michaelpmurphy14/AirQ-automation/Esp32C3 Project/3D Images/Renderred Back.png

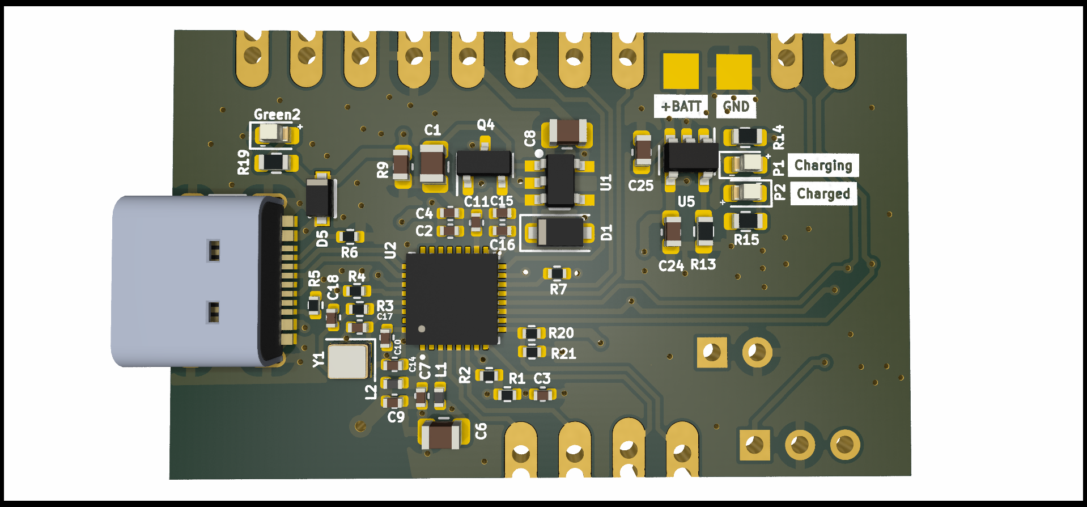
Esp32C3 Project/3D Images/Renderred Back.png
