michaelpmurphy14/AirQ-automation/CO Sensor PCB/PCB Layout.png

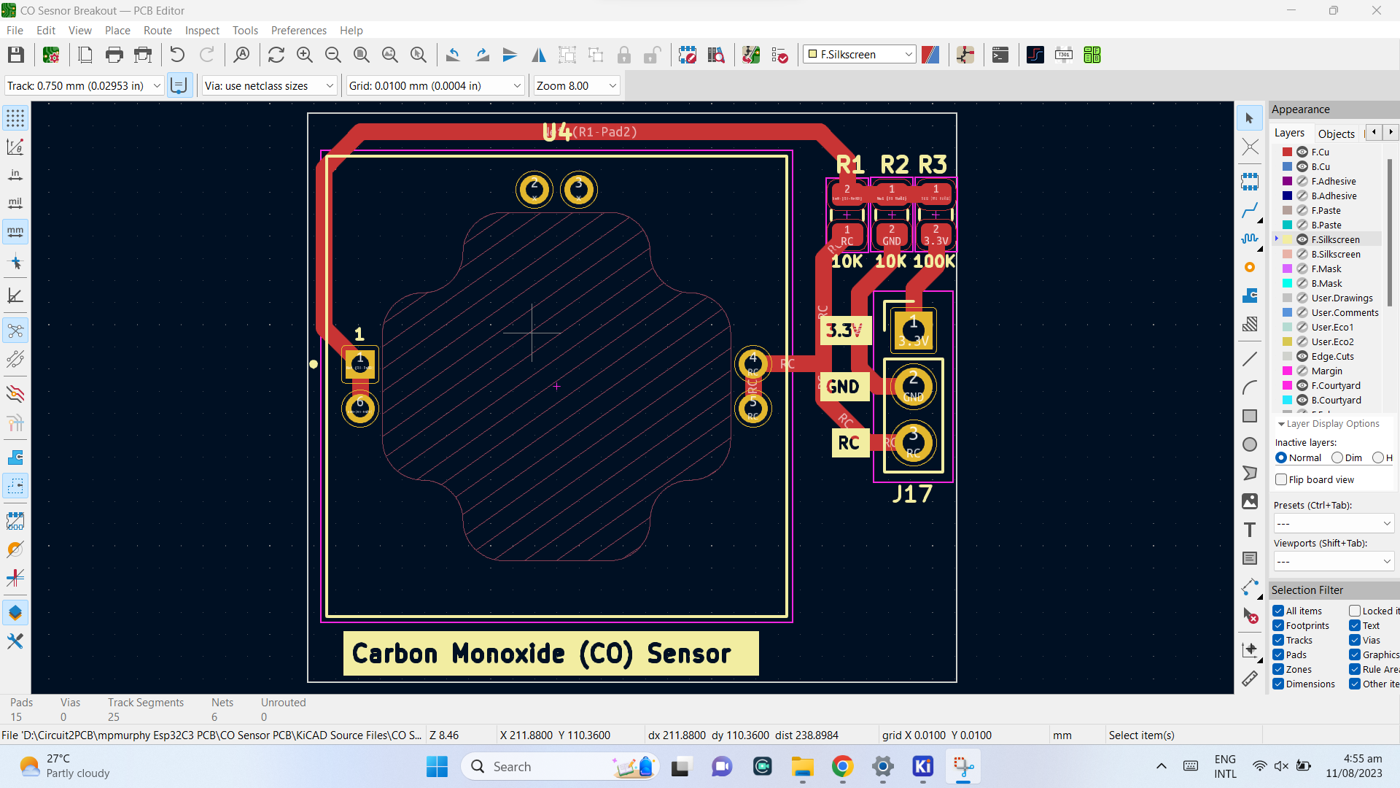
CO Sensor PCB/PCB Layout.png
