michaelpmurphy14/AirQ-automation/Esp32C3 Project/3D Images/3D.png

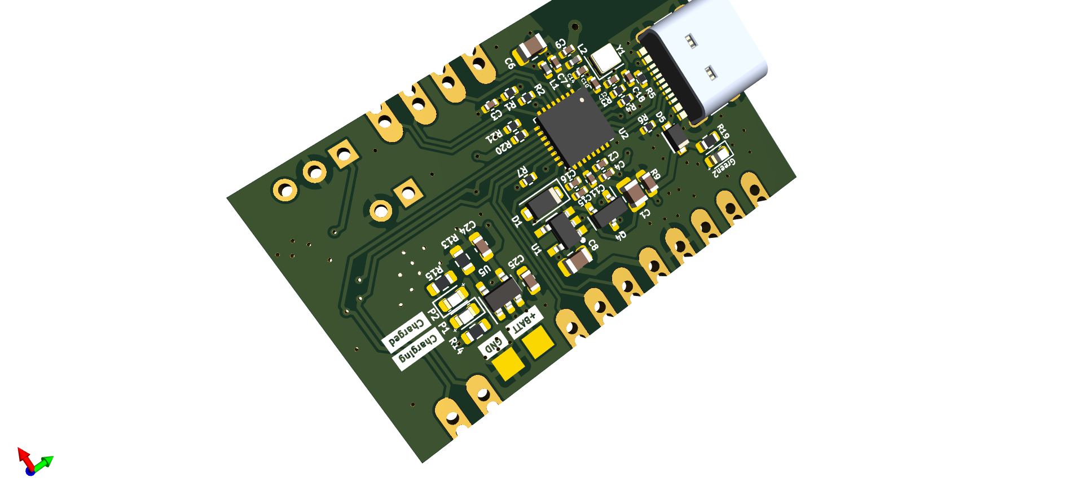
Esp32C3 Project/3D Images/3D.png
