michaelpmurphy14/AirQ-automation/Esp32C3 Project/3D Images/3DD.png

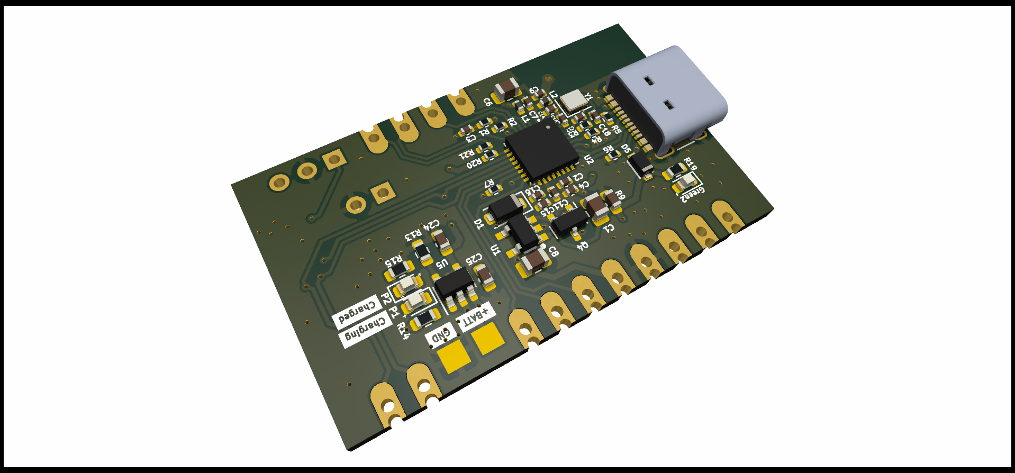
Esp32C3 Project/3D Images/3DD.png
