michaelpmurphy14/AirQ-automation/Esp32C3 Project/3D Images/Renderred Top.png

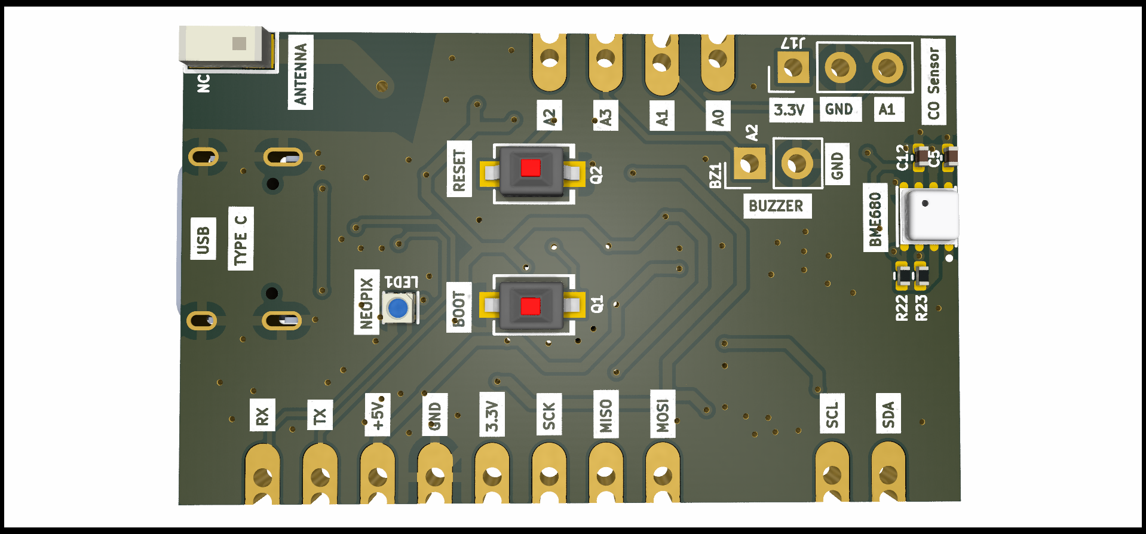
Esp32C3 Project/3D Images/Renderred Top.png
