michaelpmurphy14/AirQ-automation/Esp32C3 Project/3D Images/Top 2D.png

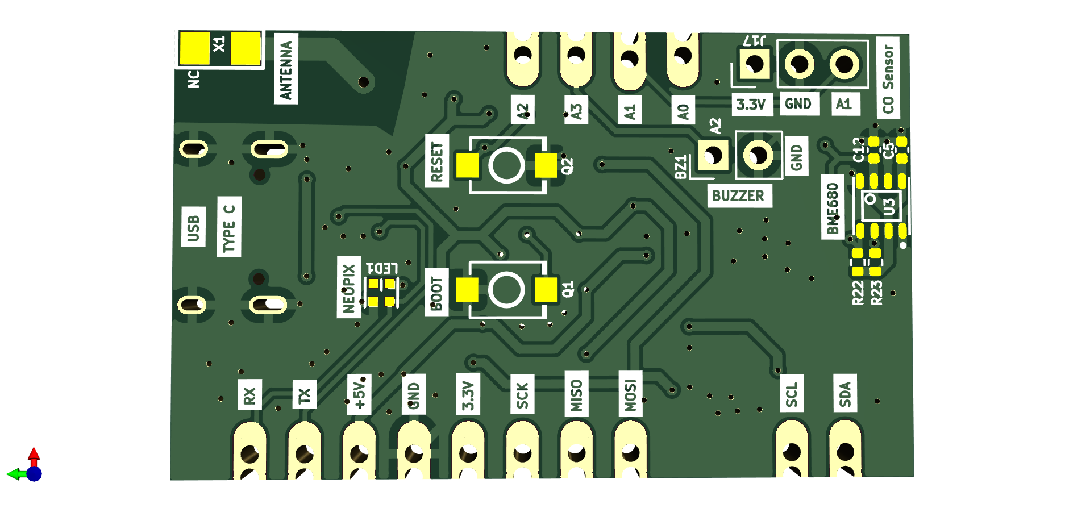
Esp32C3 Project/3D Images/Top 2D.png
