michaelpmurphy14/AirQ-automation/CO Sensor PCB/3D Step File/PCB CO Sesnor 3D v1.png

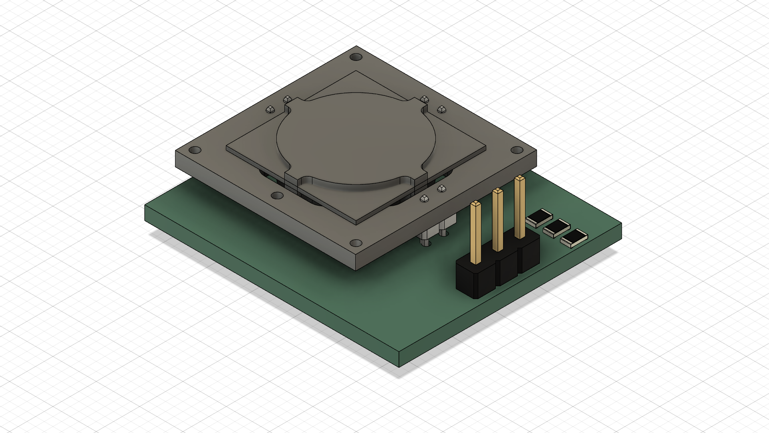
CO Sensor PCB/3D Step File/PCB CO Sesnor 3D v1.png
