michaelpmurphy14/AirQ-automation/CO Sensor PCB/3D Step File/Top.png

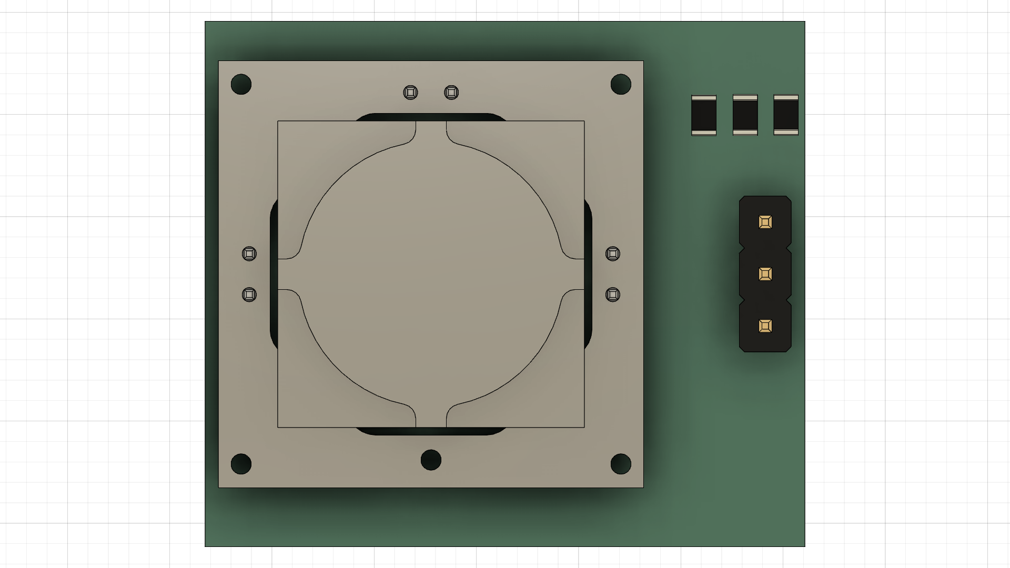
CO Sensor PCB/3D Step File/Top.png
