michaelpmurphy14/AirQ-automation/Esp32C3 Project/3D Step File/Back 3D.png

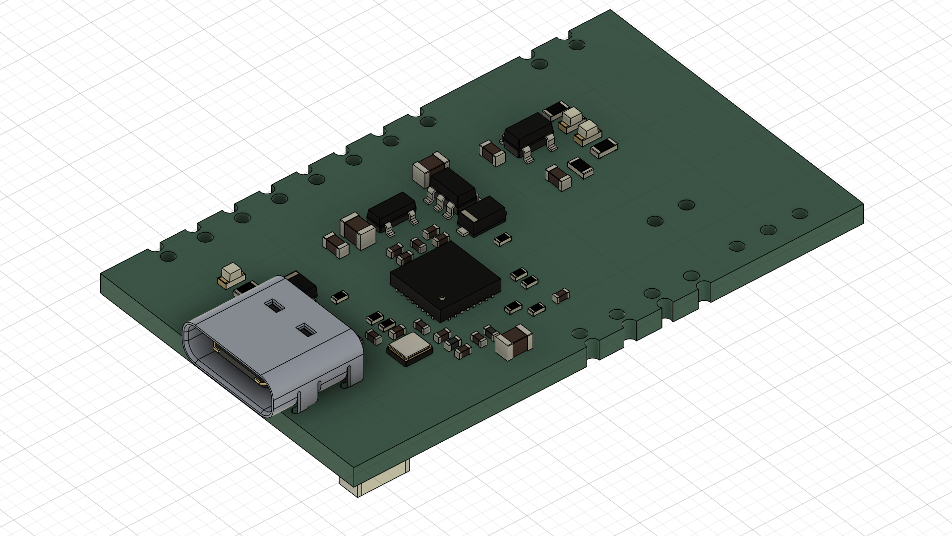
Esp32C3 Project/3D Step File/Back 3D.png
