michaelpmurphy14/AirQ-automation/Esp32C3 Project/3D Step File/sem transparent.png

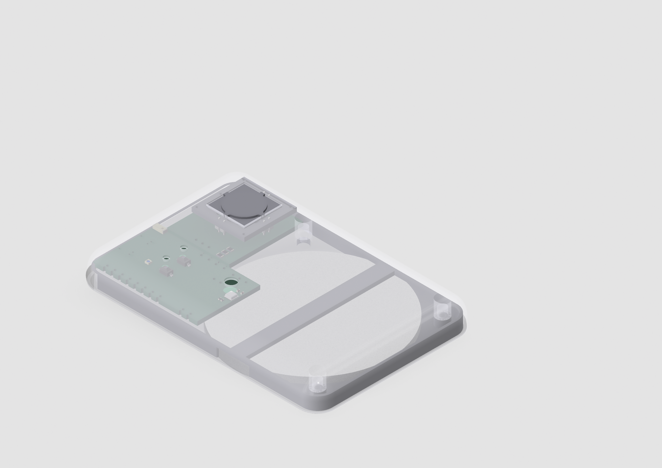
Esp32C3 Project/3D Step File/sem transparent.png
