michaelpmurphy14/AirQ-automation/Esp32C3 Project/3D Step File/Top 3D.png

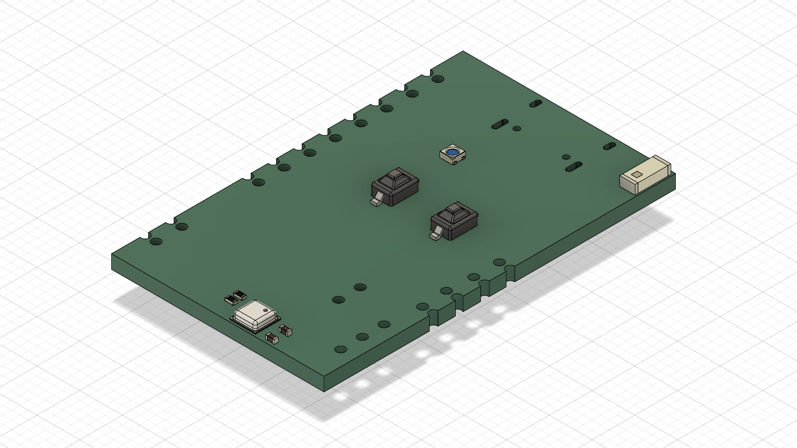
Esp32C3 Project/3D Step File/Top 3D.png
