michaelpmurphy14/AirQ-automation/CO Sensor PCB/Manufacturing & Assembly Files/Layer PDFs/CO Sesnor Breakout-B_Mask.pdf

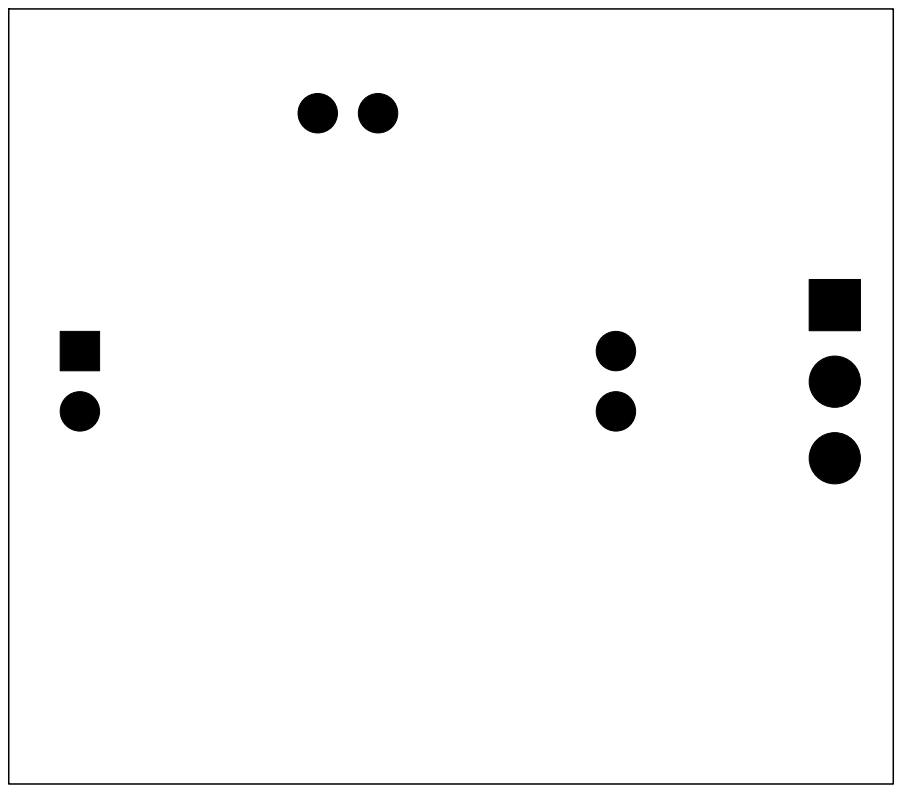
[picture p31: page 1]
