michaelpmurphy14/AirQ-automation/CO Sensor PCB/Manufacturing & Assembly Files/Layer PDFs/CO Sesnor Breakout-B_Silkscreen.pdf

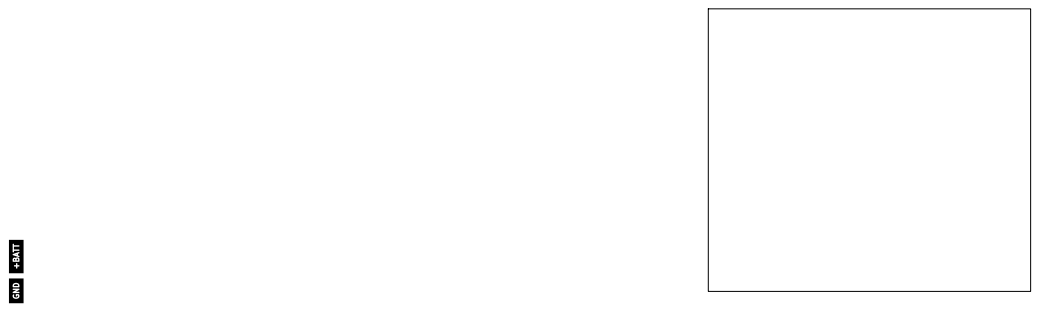
[picture p32: page 1]
