michaelpmurphy14/AirQ-automation/CO Sensor PCB/Manufacturing & Assembly Files/Layer PDFs/CO Sesnor Breakout-F_Cu.pdf

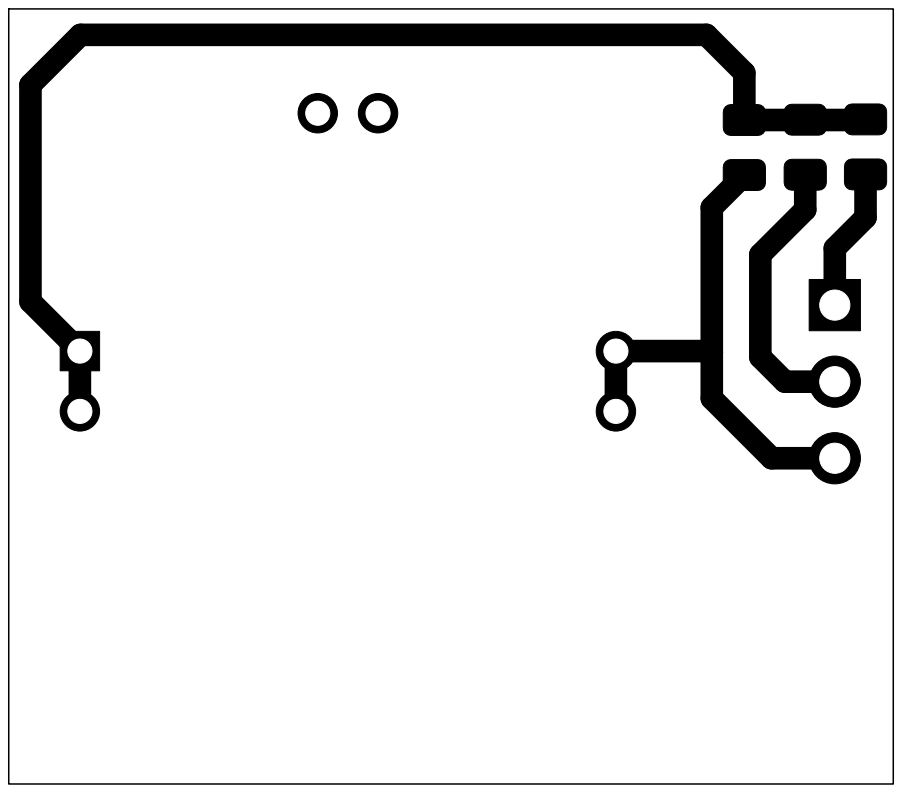
[picture p33: page 1]
