michaelpmurphy14/AirQ-automation/CO Sensor PCB/Manufacturing & Assembly Files/Layer PDFs/CO Sesnor Breakout-F_Mask.pdf

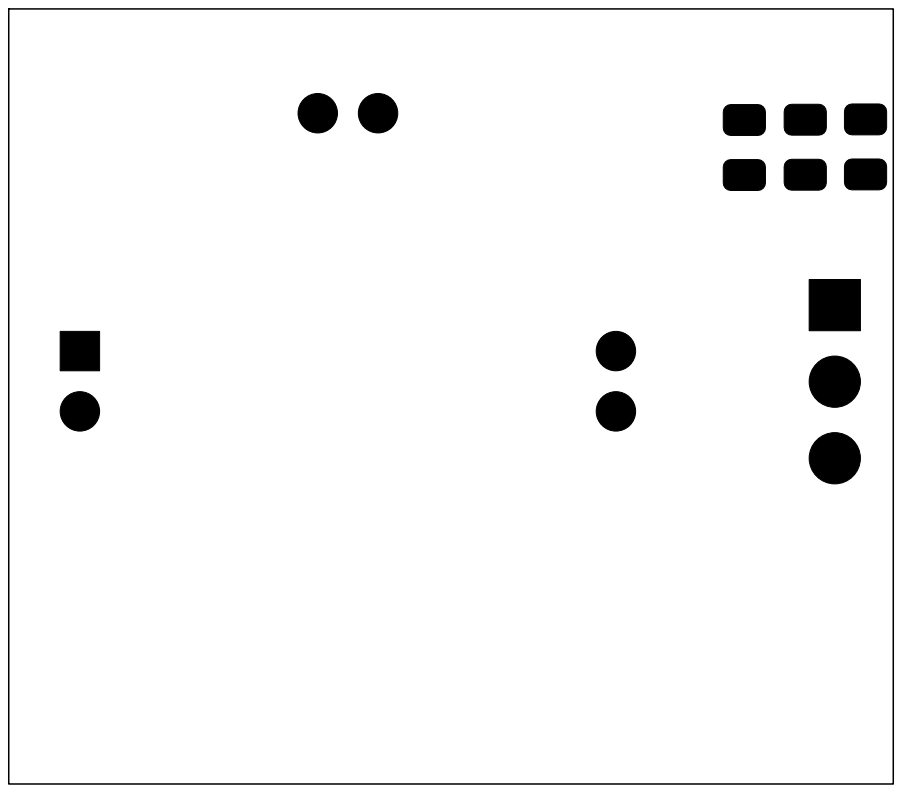
[picture p34: page 1]
