michaelpmurphy14/AirQ-automation/CO Sensor PCB/Manufacturing & Assembly Files/Layer PDFs/CO Sesnor Breakout-F_Paste.pdf

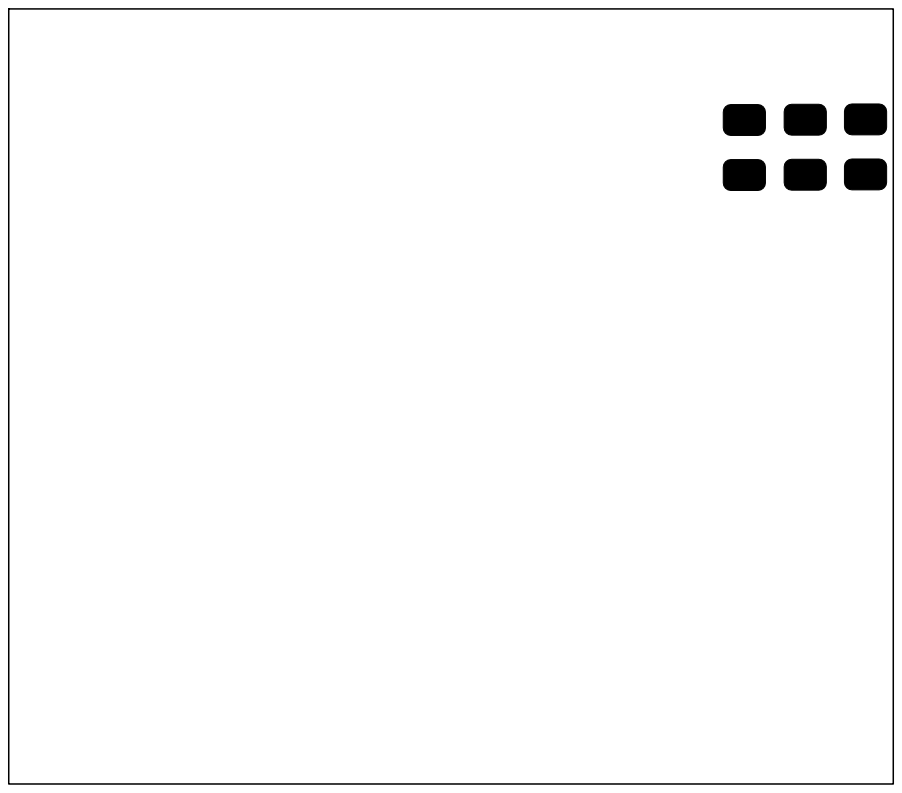
[picture p35: page 1]
